ANSIoso/SmartGlasses/glasses_software/DeviceScreen/MenuView.h

#ifndef MENUVIEW_H
#define MENUVIEW_H

#include <U8g2lib.h>

namespace MenuBitmaps {
    // 'icon_car', 32x32px
    const unsigned char epd_bitmap_icon_car [] PROGMEM = {
        0x00, 0x00, 0x00, 0x00, 0x00, 0x00, 0x00, 0x00, 0x00, 0x00, 0x00, 0x00, 0x00, 0x00, 0x00, 0x00, 
        0x00, 0x00, 0x00, 0x00, 0x00, 0x00, 0x00, 0x00, 0x00, 0x00, 0x00, 0x00, 0x00, 0x00, 0x00, 0x00, 
        0x00, 0x00, 0x00, 0x00, 0x00, 0xe0, 0x01, 0x00, 0x00, 0xf8, 0x1f, 0x00, 0x00, 0xfe, 0x3f, 0x00, 
        0x00, 0xc7, 0x38, 0x00, 0x80, 0xc3, 0x70, 0x00, 0xc0, 0xc1, 0x60, 0x00, 0xc0, 0xc1, 0xe0, 0x00, 
        0xe0, 0xe1, 0xe1, 0x00, 0xf0, 0xff, 0xff, 0x07, 0xf0, 0xff, 0xff, 0x07, 0xf0, 0xff, 0xff, 0x0f, 
        0x70, 0xf8, 0x0f, 0x0f, 0x30, 0xf3, 0x67, 0x0e, 0x80, 0x17, 0xf4, 0x00, 0x80, 0x07, 0xf0, 0x00, 
        0x00, 0x03, 0x60, 0x00, 0x00, 0x00, 0x00, 0x00, 0x00, 0x00, 0x00, 0x00, 0x00, 0x00, 0x00, 0x00, 
        0x00, 0x00, 0x00, 0x00, 0x00, 0x00, 0x00, 0x00, 0x00, 0x00, 0x00, 0x00, 0x00, 0x00, 0x00, 0x00
    };
    // 'icon_cat', 32x32px
    const unsigned char epd_bitmap_icon_cat [] PROGMEM = {
        0x00, 0x00, 0x00, 0x00, 0x00, 0x00, 0x00, 0x00, 0x00, 0x00, 0x00, 0x00, 0x00, 0x00, 0x00, 0x00, 
        0x00, 0x00, 0x00, 0x00, 0x00, 0x00, 0x00, 0x00, 0x00, 0x00, 0x00, 0x00, 0x00, 0x00, 0x00, 0x00, 
        0x00, 0x18, 0x30, 0x00, 0x00, 0x38, 0x38, 0x00, 0x00, 0xf8, 0x3f, 0x00, 0x00, 0xf8, 0x3f, 0x00, 
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
// };

// Array of all bitmaps for convenience. (Total bytes used to store images in PROGMEM = 288)
const int load_bitmaps_LEN = 2;
const unsigned char* load_bitmaps[load_bitmaps_LEN] = {
	load_bitmap_1,
	load_bitmap_2
	// load_bitmap_3
};




}

#endif
