ANSIoso/SmartGlasses/glasses_software/DeviceCamera/CameraConf.h

// ESP32-S3 Camera pins
#define PWDN_GPIO_NUM     -1
#define RESET_GPIO_NUM    -1
#define XCLK_GPIO_NUM     15
#define SIOD_GPIO_NUM     4
#define SIOC_GPIO_NUM     5
#define Y9_GPIO_NUM       16
#define Y8_GPIO_NUM       17
#define Y7_GPIO_NUM       18
#define Y6_GPIO_NUM       12
#define Y5_GPIO_NUM       10
#define Y4_GPIO_NUM       8
#define Y3_GPIO_NUM       9
#define Y2_GPIO_NUM       11
#define VSYNC_GPIO_NUM    6
#define HREF_GPIO_NUM     7
#define PCLK_GPIO_NUM     13
camera_config_t createCameraConf(){
    // definizione parametri configurazione camera  
    camera_config_t config;
    config.ledc_channel = LEDC_CHANNEL_0;
    config.ledc_timer = LEDC_TIMER_0;
    config.pin_d0 = Y2_GPIO_NUM;
    config.pin_d1 = Y3_GPIO_NUM;
    config.pin_d2 = Y4_GPIO_NUM;
    config.pin_d3 = Y5_GPIO_NUM;
    config.pin_d4 = Y6_GPIO_NUM;
    config.pin_d5 = Y7_GPIO_NUM;
    config.pin_d6 = Y8_GPIO_NUM;
    config.pin_d7 = Y9_GPIO_NUM;
    config.pin_xclk = XCLK_GPIO_NUM;
    config.pin_pclk = PCLK_GPIO_NUM;
    config.pin_vsync = VSYNC_GPIO_NUM;
    config.pin_href = HREF_GPIO_NUM;
    config.pin_sscb_sda = SIOD_GPIO_NUM;
    config.pin_sscb_scl = SIOC_GPIO_NUM;
    config.pin_pwdn = PWDN_GPIO_NUM;
    config.pin_reset = RESET_GPIO_NUM;
    config.xclk_freq_hz = 20000000;
    config.pixel_format = PIXFORMAT_JPEG;
    config.grab_mode = CAMERA_GRAB_WHEN_EMPTY;
    
    // settaggi qualità/velicità
    config.fb_count = 1;

    if(psramFound()){
      config.frame_size = FRAMESIZE_VGA;
      config.jpeg_quality = 15;

      //config.frame_size = FRAMESIZE_240X240;
      //config.jpeg_quality = 20;


      config.fb_location = CAMERA_FB_IN_PSRAM;
    }else{
      config.frame_size = FRAMESIZE_QVGA;
      config.jpeg_quality = 25;
      config.fb_location = CAMERA_FB_IN_DRAM;
    }
    return config;
}
